franckklotz/Robotic-Ventilator/3D rendering/Capture d’écran, le 2020-03-31 à 14.56.32.png

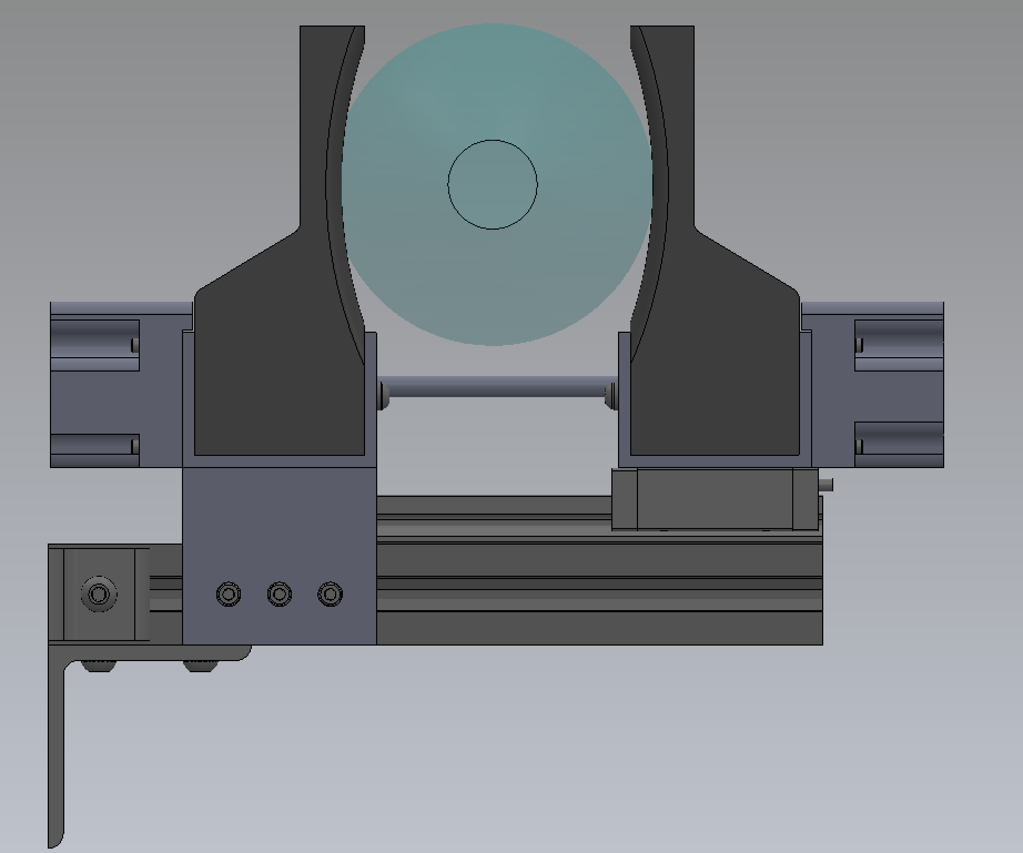
3D rendering/Capture d’écran, le 2020-03-31 à 14.56.32.png
