franckklotz/Robotic-Ventilator/3D rendering/Capture d’écran, le 2020-03-31 à 15.00.58.png

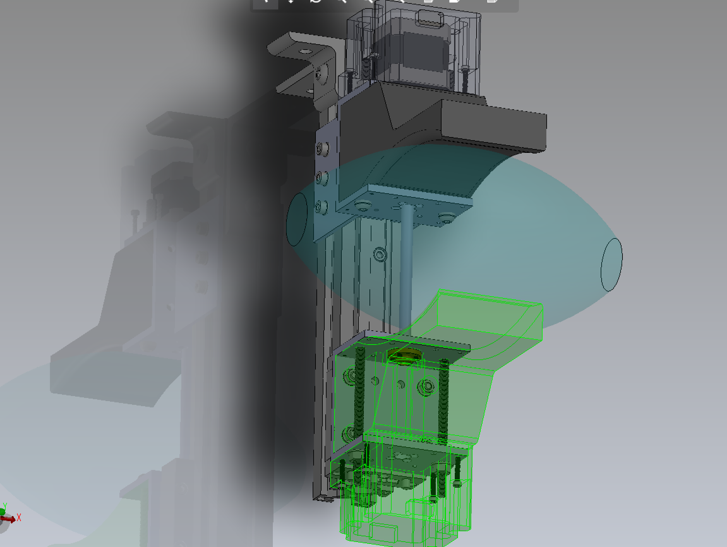
3D rendering/Capture d’écran, le 2020-03-31 à 15.00.58.png
