franckklotz/Robotic-Ventilator/mechanical parts/ALUMINUM EXTRUSION HARDWARE - ROBOUNITS-TIN-4508 - M8 NUT.sldprt

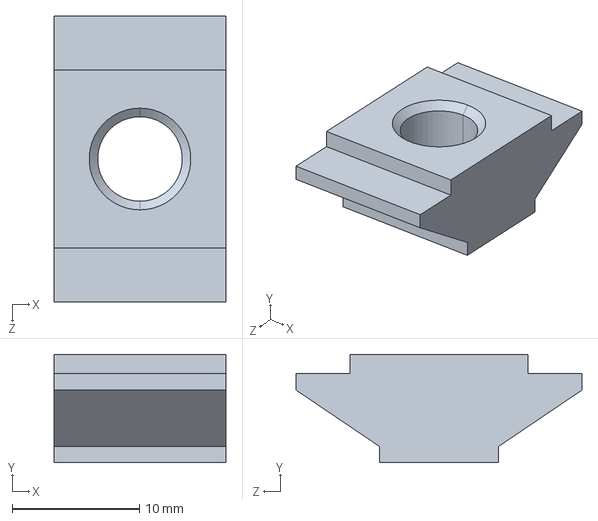
[picture p27: CAD file, 2020-03-31]
mechanical parts/ALUMINUM EXTRUSION HARDWARE - ROBOUNITS-TIN-4508 - M8 NUT.sldprt
13.5 x 8.50 x 22.5 mm
