franckklotz/Robotic-Ventilator/mechanical parts/92095A129_BUTTON HEAD HEX DRIVE SCREW.SLDPRT

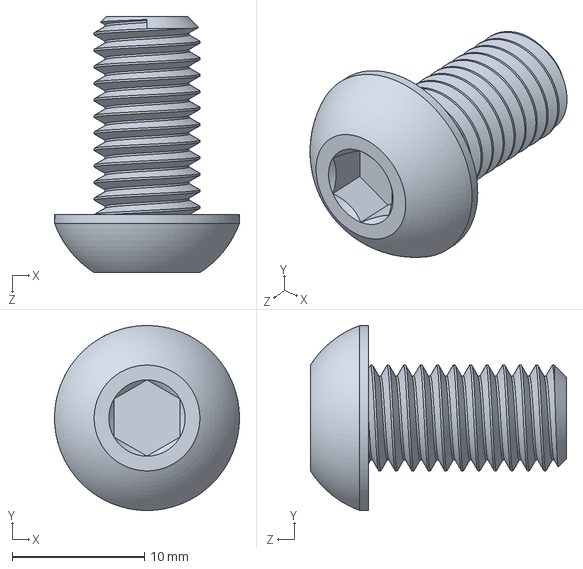
[picture p28: CAD file, 2020-03-31]
mechanical parts/92095A129_BUTTON HEAD HEX DRIVE SCREW.SLDPRT
14.0 x 14.0 x 19.4 mm
