franckklotz/Robotic-Ventilator/mechanical parts/ENV - NUT LEAD SCREW POLOLU 2688.SLDPRT

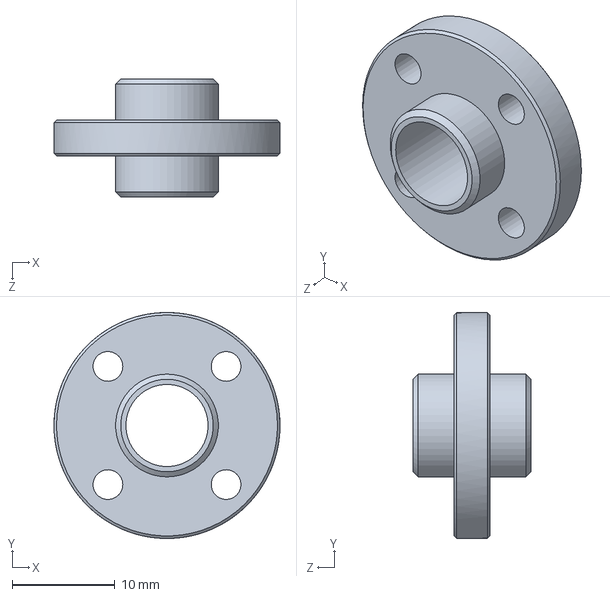
[picture p29: CAD file, 2020-03-31]
mechanical parts/ENV - NUT LEAD SCREW POLOLU 2688.SLDPRT
22.0 x 22.0 x 11.5 mm
