franckklotz/Robotic-Ventilator/mechanical parts/92290A867_SUPER-CORROSION-RST 316 SS SCKT HEAD SCREW.SLDPRT

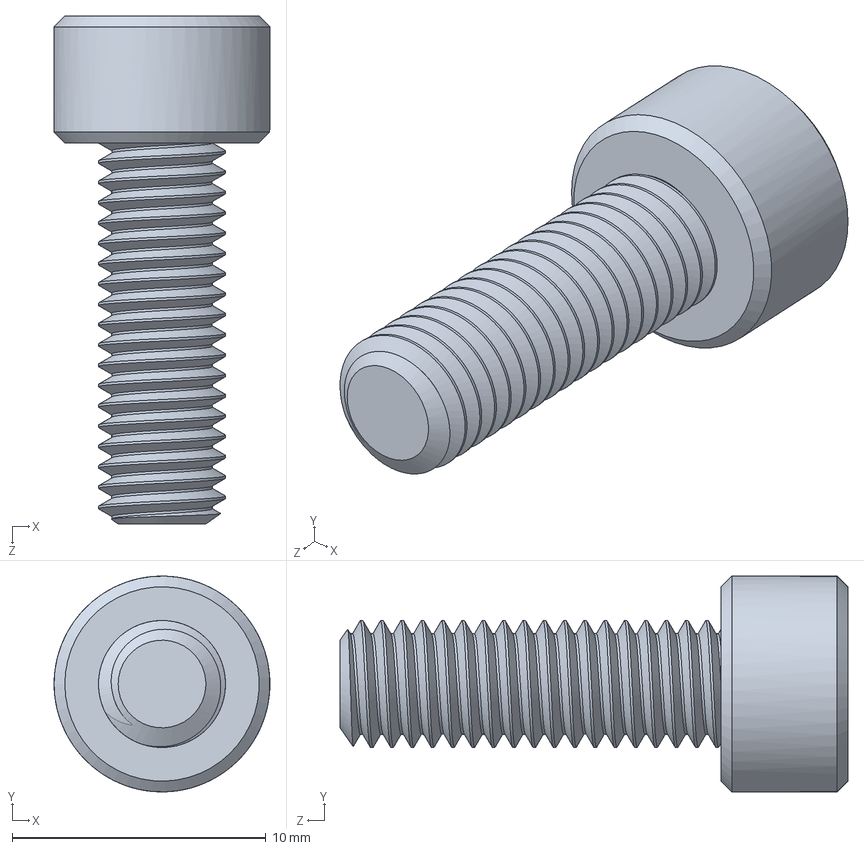
[picture p30: CAD file, 2020-03-31]
mechanical parts/92290A867_SUPER-CORROSION-RST 316 SS SCKT HEAD SCREW.SLDPRT
8.50 x 8.50 x 20.0 mm
